balthazar-space/Balthazar-IO/images/BalthazarIO_5.png

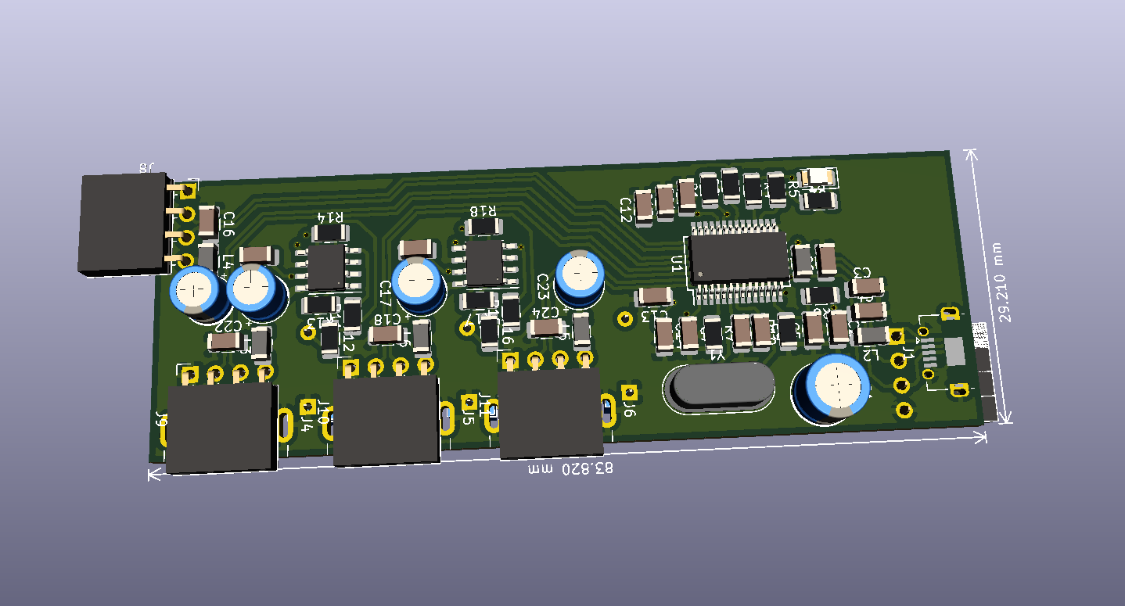
images/BalthazarIO_5.png
